VinCSS-Public-Projects/FlexiCAN/1.firmware/rp2040/external_libs/CherryUSB/docs/assets/usb_outline.png

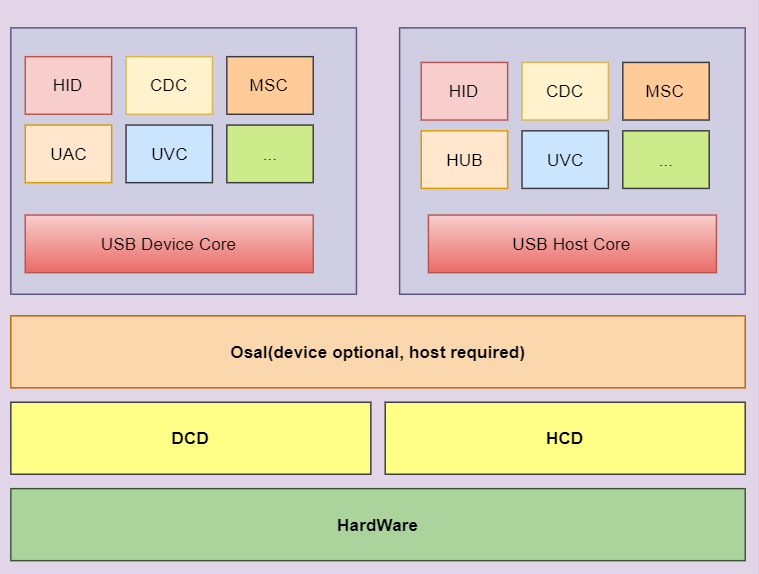
1.firmware/rp2040/external_libs/CherryUSB/docs/assets/usb_outline.png
