VinCSS-Public-Projects/FlexiCAN/1.firmware/rp2040/external_libs/CherryUSB/docs/source/api/img/api_device1.png

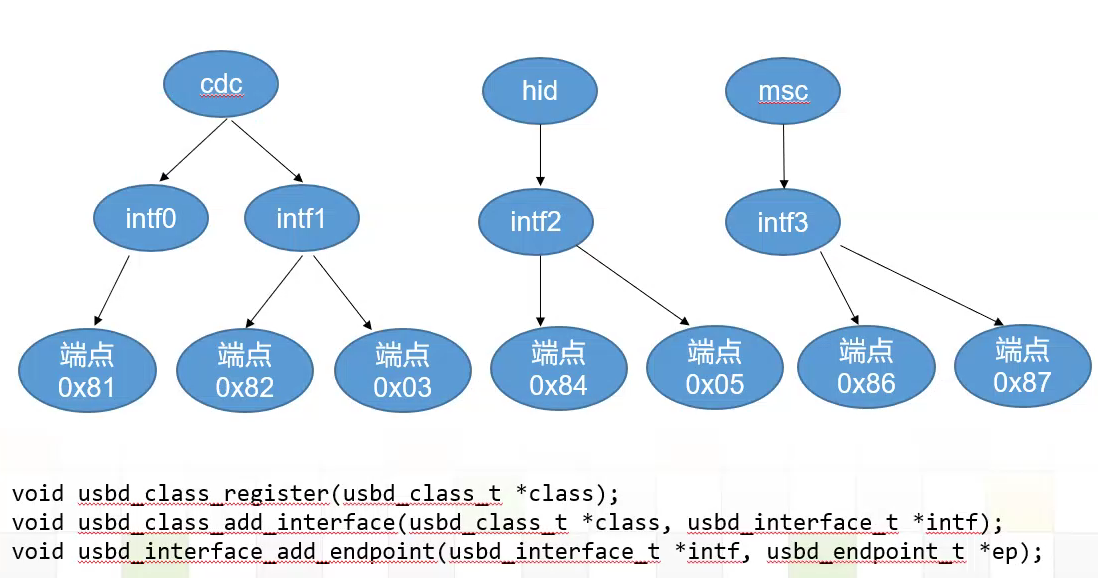
1.firmware/rp2040/external_libs/CherryUSB/docs/source/api/img/api_device1.png
