VinCSS-Public-Projects/FlexiCAN/1.firmware/rp2040/external_libs/CherryUSB/docs/source/quick_start/img/stm32_10.png

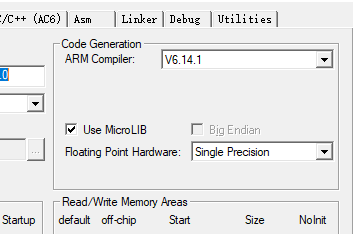
1.firmware/rp2040/external_libs/CherryUSB/docs/source/quick_start/img/stm32_10.png
