VinCSS-Public-Projects/FlexiCAN/1.firmware/rp2040/external_libs/CherryUSB/docs/source/quick_start/rt-thread/img/config_file.png

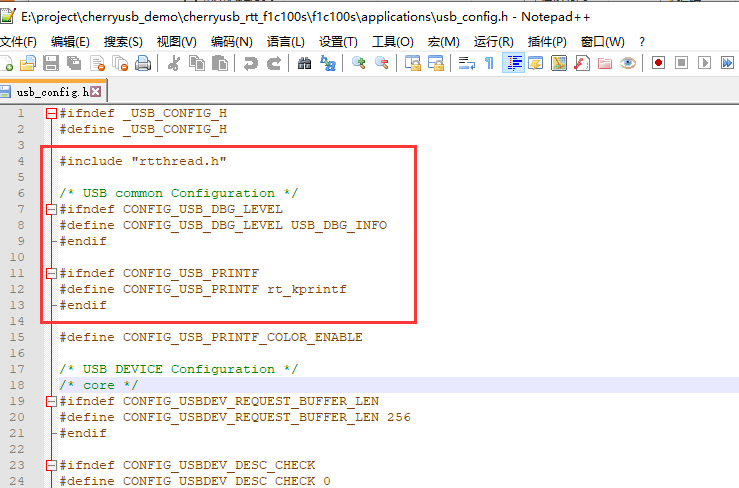
1.firmware/rp2040/external_libs/CherryUSB/docs/source/quick_start/rt-thread/img/config_file.png
