VinCSS-Public-Projects/FlexiCAN/1.firmware/rp2040/external_libs/CherryUSB/docs/source/tools/img/chrytool5.png

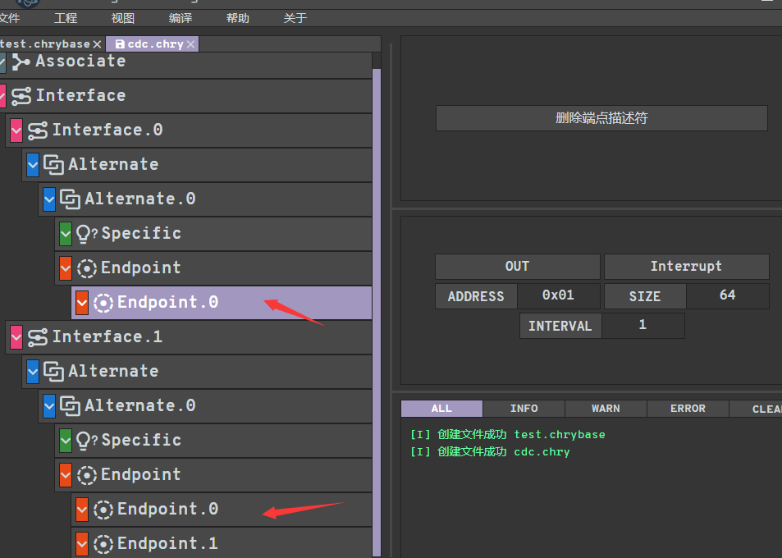
1.firmware/rp2040/external_libs/CherryUSB/docs/source/tools/img/chrytool5.png
