VinCSS-Public-Projects/FlexiCAN/1.firmware/rp2040/external_libs/CherryUSB/docs/source/usb/img/1.png

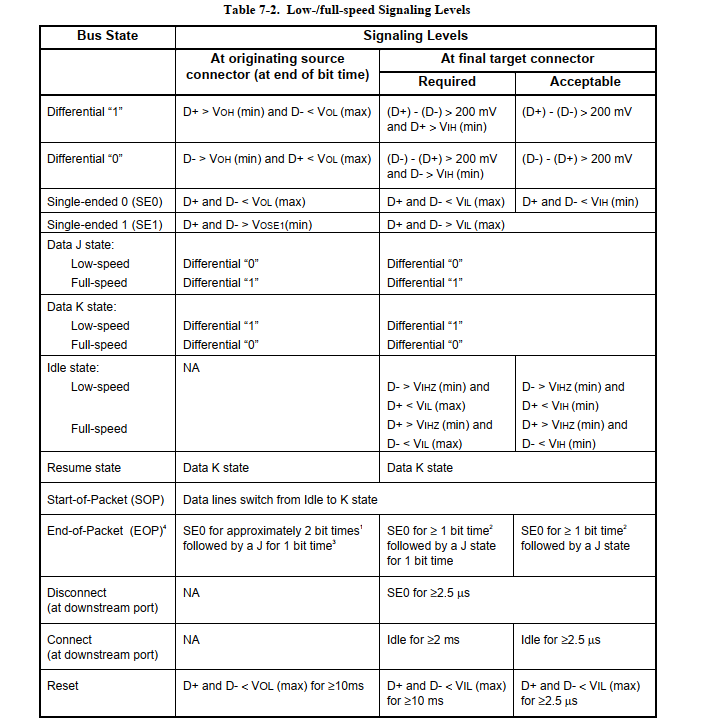
1.firmware/rp2040/external_libs/CherryUSB/docs/source/usb/img/1.png
