VinCSS-Public-Projects/FlexiCAN/1.firmware/rp2040/external_libs/CherrySH/doc/test2.png

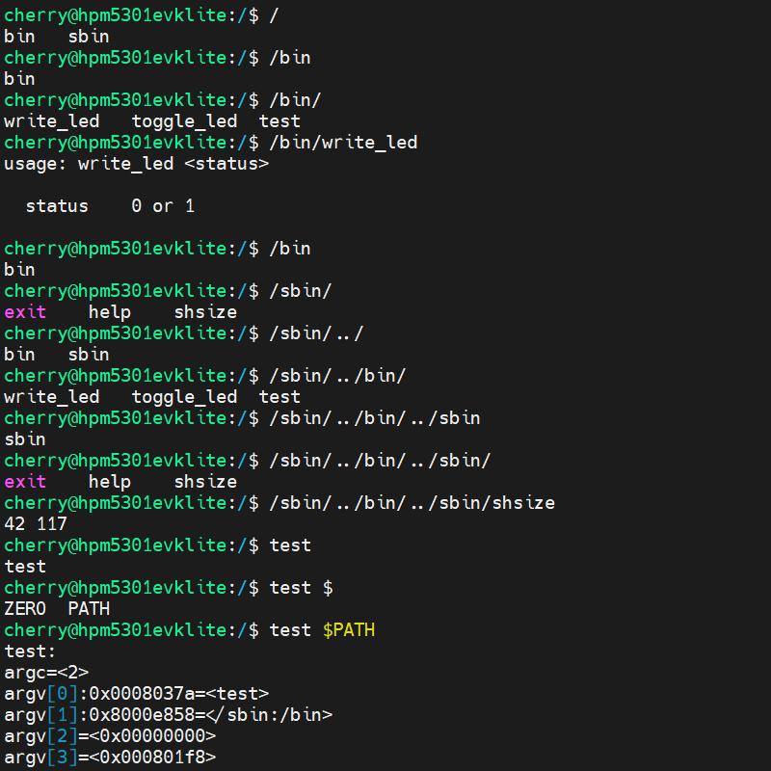
1.firmware/rp2040/external_libs/CherrySH/doc/test2.png
