VinCSS-Public-Projects/FlexiCAN/1.firmware/stm32/src/boards/g431-Obit_FDCAN.c

/*

The MIT License (MIT)

Copyright (c) 2024 Quantulum Ltd,
              Phil Greenland <phil@quantulum.co.uk>

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
*/

#include "board.h"
#include "config.h"
#include "device.h"
#include "gpio.h"
#include "led.h"
#include "usbd_gs_can.h"

#define LEDRX_GPIO_Port	  GPIOC
#define LEDRX_Pin		  GPIO_PIN_6
#define LEDRX_Mode		  GPIO_MODE_OUTPUT_PP
#define LEDRX_Active_High 1

#define LEDTX_GPIO_Port	  GPIOB
#define LEDTX_Pin		  GPIO_PIN_12
#define LEDTX_Mode		  GPIO_MODE_OUTPUT_PP
#define LEDTX_Active_High 1

#include <stdio.h>
#include <stdint.h>
#include <string.h>

char obit_product_string[64] = {0};
char obit_interface_string[64] = {0};

static void detect_can_id(uint8_t bit2, uint8_t bit1, uint8_t bit0)
{
	uint8_t can_id = 0;
	uint32_t uid = HAL_GetUIDw0();
	uint32_t uid1 = HAL_GetUIDw1();
	uid = uid ^ uid1;
	can_id = (bit2 << 2) | (bit1 << 1) | bit0;
	memset(obit_product_string, 0, sizeof(obit_product_string));
	memset(obit_interface_string, 0, sizeof(obit_interface_string));
	snprintf(obit_product_string, sizeof(obit_product_string), "VinCSS OBD-II CAN id %lx channel %u gs_usb id ", uid, can_id);
	snprintf(obit_interface_string, sizeof(obit_interface_string), "VinCSS OBD-II CAN id %lx channel %u firmware upgrade interface", uid, can_id);
}

static void obit_fdcan_setup(USBD_GS_CAN_HandleTypeDef *hcan)
{
	GPIO_InitTypeDef GPIO_InitStruct;

	UNUSED(hcan);

	__HAL_RCC_GPIOA_CLK_ENABLE();
	__HAL_RCC_GPIOB_CLK_ENABLE();
	__HAL_RCC_GPIOC_CLK_ENABLE();

	/* LEDs */

	HAL_GPIO_WritePin(GPIOB, GPIO_PIN_3, 0);
	HAL_GPIO_WritePin(GPIOB, GPIO_PIN_4, 0);
	HAL_GPIO_WritePin(GPIOB, GPIO_PIN_5, 0);
	HAL_GPIO_WritePin(GPIOB, GPIO_PIN_6, 0);
	HAL_GPIO_WritePin(GPIOB, GPIO_PIN_7, 0);

	HAL_GPIO_WritePin(LEDRX_GPIO_Port, LEDRX_Pin, GPIO_INIT_STATE(LEDRX_Active_High));
	GPIO_InitStruct.Pin = LEDRX_Pin;
	GPIO_InitStruct.Mode = LEDRX_Mode;
	GPIO_InitStruct.Pull = GPIO_NOPULL;
	GPIO_InitStruct.Speed = GPIO_SPEED_FREQ_HIGH;
	HAL_GPIO_Init(LEDRX_GPIO_Port, &GPIO_InitStruct);

	HAL_GPIO_WritePin(LEDTX_GPIO_Port, LEDTX_Pin, GPIO_INIT_STATE(LEDTX_Active_High));
	GPIO_InitStruct.Pin = LEDTX_Pin;
	GPIO_InitStruct.Mode = LEDTX_Mode;
	GPIO_InitStruct.Pull = GPIO_NOPULL;
	GPIO_InitStruct.Speed = GPIO_SPEED_FREQ_HIGH;
	HAL_GPIO_Init(LEDTX_GPIO_Port, &GPIO_InitStruct);

	HAL_GPIO_WritePin(LEDRX_GPIO_Port, LEDRX_Pin, 1);
	HAL_GPIO_WritePin(LEDRX_GPIO_Port, LEDTX_Pin, 1);

	// Init can STB pin
	HAL_GPIO_WritePin(GPIOC, GPIO_PIN_14, 0);
	GPIO_InitStruct.Pin = GPIO_PIN_14;
	GPIO_InitStruct.Mode = GPIO_MODE_OUTPUT_PP;
	GPIO_InitStruct.Pull = GPIO_PULLDOWN;
	GPIO_InitStruct.Speed = GPIO_SPEED_FREQ_HIGH;
	HAL_GPIO_Init(GPIOC, &GPIO_InitStruct);
	HAL_GPIO_WritePin(GPIOC, GPIO_PIN_14, 0);
	HAL_GPIO_WritePin(GPIOC, GPIO_PIN_14, 0);

	//Init GPIO for detect position can
	GPIO_InitStruct.Pin = GPIO_PIN_2;
	GPIO_InitStruct.Mode = GPIO_MODE_INPUT;
	GPIO_InitStruct.Pull = GPIO_PULLUP;
	GPIO_InitStruct.Speed = GPIO_SPEED_FREQ_HIGH;
	HAL_GPIO_Init(GPIOA, &GPIO_InitStruct);
	GPIO_InitStruct.Pin = GPIO_PIN_3;
	GPIO_InitStruct.Mode = GPIO_MODE_INPUT;
	GPIO_InitStruct.Pull = GPIO_PULLUP;
	GPIO_InitStruct.Speed = GPIO_SPEED_FREQ_HIGH;
	HAL_GPIO_Init(GPIOA, &GPIO_InitStruct);
	GPIO_InitStruct.Pin = GPIO_PIN_4;
	GPIO_InitStruct.Mode = GPIO_MODE_INPUT;
	GPIO_InitStruct.Pull = GPIO_PULLUP;
	GPIO_InitStruct.Speed = GPIO_SPEED_FREQ_HIGH;
	HAL_GPIO_Init(GPIOA, &GPIO_InitStruct);

	uint8_t bit2=0, bit1=0, bit0=0;

	bit2 = (uint8_t)HAL_GPIO_ReadPin(GPIOA, GPIO_PIN_2);
	bit1 = (uint8_t)HAL_GPIO_ReadPin(GPIOA, GPIO_PIN_3);
	bit0 = (uint8_t)HAL_GPIO_ReadPin(GPIOA, GPIO_PIN_4);

	detect_can_id(bit2, bit1, bit0);

	uint32_t delay_time = (bit2 << 2) | (bit1 << 1) | bit0;
	delay_time = delay_time * 50;

	HAL_Delay(delay_time);
	// Init CAN VIO

	GPIO_InitStruct.Pin = GPIO_PIN_3;
	GPIO_InitStruct.Mode = GPIO_MODE_OUTPUT_PP;
	GPIO_InitStruct.Pull = GPIO_PULLUP;
	GPIO_InitStruct.Speed = GPIO_SPEED_FREQ_HIGH;
	HAL_GPIO_Init(GPIOB, &GPIO_InitStruct);
	HAL_GPIO_WritePin(GPIOB, GPIO_PIN_3, 1);

	GPIO_InitStruct.Pin = GPIO_PIN_4;
	GPIO_InitStruct.Mode = GPIO_MODE_OUTPUT_PP;
	GPIO_InitStruct.Pull = GPIO_PULLUP;
	GPIO_InitStruct.Speed = GPIO_SPEED_FREQ_HIGH;
	HAL_GPIO_Init(GPIOB, &GPIO_InitStruct);
	HAL_GPIO_WritePin(GPIOB, GPIO_PIN_4, 1);

	GPIO_InitStruct.Pin = GPIO_PIN_5;
	GPIO_InitStruct.Mode = GPIO_MODE_OUTPUT_PP;
	GPIO_InitStruct.Pull = GPIO_PULLUP;
	GPIO_InitStruct.Speed = GPIO_SPEED_FREQ_HIGH;
	HAL_GPIO_Init(GPIOB, &GPIO_InitStruct);
	HAL_GPIO_WritePin(GPIOB, GPIO_PIN_5, 1);

	GPIO_InitStruct.Pin = GPIO_PIN_6;
	GPIO_InitStruct.Mode = GPIO_MODE_OUTPUT_PP;
	GPIO_InitStruct.Pull = GPIO_PULLUP;
	GPIO_InitStruct.Speed = GPIO_SPEED_FREQ_HIGH;
	HAL_GPIO_Init(GPIOB, &GPIO_InitStruct);
	HAL_GPIO_WritePin(GPIOB, GPIO_PIN_6, 1);

	GPIO_InitStruct.Pin = GPIO_PIN_7;
	GPIO_InitStruct.Mode = GPIO_MODE_OUTPUT_PP;
	GPIO_InitStruct.Pull = GPIO_PULLUP;
	GPIO_InitStruct.Speed = GPIO_SPEED_FREQ_HIGH;
	HAL_GPIO_Init(GPIOB, &GPIO_InitStruct);
	HAL_GPIO_WritePin(GPIOB, GPIO_PIN_7, 1);



	/* FDCAN */

	RCC_PeriphCLKInitTypeDef PeriphClkInit = {
		.PeriphClockSelection = RCC_PERIPHCLK_FDCAN,
		.FdcanClockSelection = RCC_FDCANCLKSOURCE_PCLK1,
	};

	HAL_RCCEx_PeriphCLKConfig(&PeriphClkInit);
	__HAL_RCC_FDCAN_CLK_ENABLE();

	/* FDCAN1_RX, FDCAN1_TX */
	GPIO_InitStruct.Pin = GPIO_PIN_9 | GPIO_PIN_8;
	GPIO_InitStruct.Mode = GPIO_MODE_AF_PP;
	GPIO_InitStruct.Pull = GPIO_NOPULL;
	GPIO_InitStruct.Speed = GPIO_SPEED_FREQ_HIGH;
	GPIO_InitStruct.Alternate = GPIO_AF9_FDCAN1;
	HAL_GPIO_Init(GPIOB, &GPIO_InitStruct);
}


static void obit_fdcan_phy_power_set(can_data_t *channel, bool enable)
{
	UNUSED(channel);
	UNUSED(enable);
}

static void obit_fdcan_termination_set(can_data_t *channel, enum gs_can_termination_state enable)
{
	UNUSED(channel);
	UNUSED(enable);
}

static void obit_fdcan_mainloop_callback (void)
{

}

const struct BoardConfig config = {
	.setup = obit_fdcan_setup,
	.phy_power_set = obit_fdcan_phy_power_set,
	.termination_set = obit_fdcan_termination_set,
	.mainloop_callback = obit_fdcan_mainloop_callback,
	.channels[0] = {
		.interface = FDCAN1,
		.leds = {
			[LED_RX] = {
				.port = LEDRX_GPIO_Port,
				.pin = LEDRX_Pin,
				.active_high = LEDRX_Active_High,
			},
			[LED_TX] = {
				.port = LEDTX_GPIO_Port,
				.pin = LEDTX_Pin,
				.active_high = LEDTX_Active_High,
			},
		},
	},
};
