VinCSS-Public-Projects/FlexiCAN/1.firmware/rp2040/include/logo.h

#ifndef __INC_IMAGE_LOGO
#define __INC_IMAGE_LOGO

const unsigned long logo_image_size=2511;
const unsigned char logo_image_data[] = {
// 'Screenshot_2024-08-01_220146-rem', 81x31px
0xff, 0xff, 0xff, 0xff, 0xff, 0xff, 0xff, 0xff, 0xff, 0xff, 0x80, 
    0xff, 0xff, 0xff, 0xff, 0xff, 0xff, 0xff, 0xff, 0xff, 0xff, 0x80, 
    0xff, 0xff, 0xff, 0xff, 0xff, 0xff, 0xff, 0xff, 0xff, 0xff, 0x80, 
    0xff, 0xff, 0xff, 0xff, 0xff, 0xff, 0xff, 0xff, 0xff, 0xff, 0x80, 
    0xff, 0xff, 0xff, 0xff, 0xff, 0xff, 0xff, 0xff, 0xff, 0xff, 0x80, 
    0xff, 0xff, 0xff, 0xff, 0xff, 0xff, 0xff, 0xff, 0xff, 0xff, 0x80, 
    0xff, 0xff, 0xff, 0xff, 0xff, 0xff, 0xff, 0xff, 0xff, 0xff, 0x80, 
    0xff, 0xff, 0xff, 0xff, 0xff, 0xff, 0xff, 0xff, 0xff, 0xff, 0x80, 
    0xff, 0xff, 0xff, 0xff, 0xff, 0xff, 0xff, 0xff, 0xff, 0xff, 0x80, 
    0xff, 0xff, 0xff, 0xff, 0xff, 0xff, 0xff, 0xff, 0xff, 0xff, 0x80, 
    0xff, 0xff, 0xff, 0xff, 0xff, 0xff, 0xff, 0xff, 0xff, 0xff, 0x80, 
    0xff, 0xff, 0xff, 0xff, 0xff, 0xff, 0xff, 0xff, 0xff, 0xff, 0x80, 
    0xff, 0xff, 0xff, 0xff, 0xff, 0xff, 0xff, 0xff, 0xff, 0xff, 0x80, 
    0xff, 0x7f, 0x3b, 0x1f, 0xbc, 0x01, 0xd0, 0x1e, 0x01, 0xff, 0x80, 
    0xfe, 0x7e, 0x73, 0x07, 0x99, 0x55, 0xc5, 0x5c, 0xaa, 0xff, 0x80, 
    0xff, 0x7c, 0xfb, 0x67, 0xb3, 0xff, 0x9f, 0xf9, 0xff, 0xff, 0x80, 
    0xfe, 0x79, 0xf3, 0x33, 0x9b, 0xff, 0x88, 0x3c, 0x03, 0xff, 0x80, 
    0xfe, 0x73, 0xfb, 0x39, 0xb3, 0xff, 0xe2, 0x9e, 0x50, 0xff, 0x80, 
    0xff, 0x67, 0xf3, 0x79, 0x99, 0xff, 0xff, 0xcf, 0xfc, 0xff, 0x80, 
    0xfe, 0x0f, 0xf3, 0x3c, 0x38, 0x03, 0xc8, 0x1c, 0x08, 0xff, 0x80, 
    0xff, 0x2f, 0xfb, 0x7e, 0xbd, 0x69, 0xa5, 0x5d, 0x53, 0xff, 0x80, 
    0xff, 0xff, 0xff, 0xff, 0xff, 0xff, 0xff, 0xff, 0xff, 0xff, 0x80, 
    0xff, 0xff, 0xff, 0xff, 0xff, 0xff, 0xff, 0xff, 0xff, 0xff, 0x80, 
    0xff, 0xff, 0xff, 0xff, 0xff, 0xff, 0xff, 0xff, 0xff, 0xff, 0x80, 
    0xff, 0xff, 0xff, 0xff, 0xff, 0xff, 0xff, 0xff, 0xff, 0xff, 0x80, 
    0xff, 0xff, 0xff, 0xff, 0xff, 0xff, 0xff, 0xff, 0xff, 0xff, 0x80, 
    0xff, 0xff, 0xff, 0xff, 0xff, 0xff, 0xff, 0xff, 0xff, 0xff, 0x80, 
    0xff, 0xff, 0xff, 0xff, 0xff, 0xff, 0xff, 0xff, 0xff, 0xff, 0x80, 
    0xff, 0xff, 0xff, 0xff, 0xff, 0xff, 0xff, 0xff, 0xff, 0xff, 0x80, 
    0xff, 0xff, 0xff, 0xff, 0xff, 0xff, 0xff, 0xff, 0xff, 0xff, 0x80, 
    0xff, 0xff, 0xff, 0xff, 0xff, 0xff, 0xff, 0xff, 0xff, 0xff, 0x80
};

#endif
